nimitvijayvargee/zepto_duo_terminal/images/image-5.png

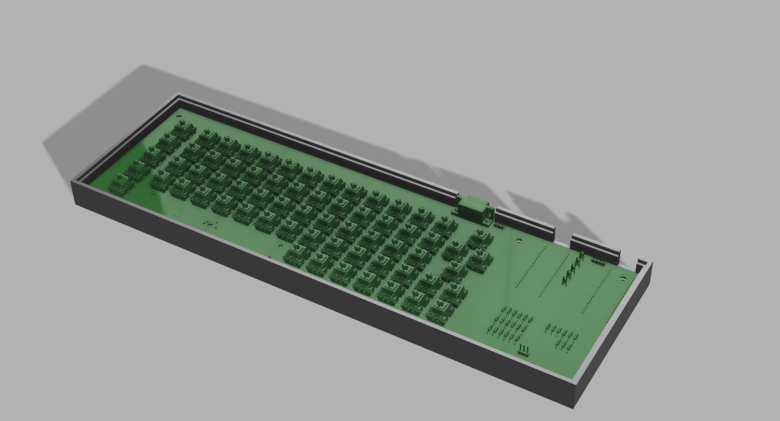
images/image-5.png
